citixen/starseq/controller/crc8.cpp

// =============================================================================
//  crc8.cpp — Shared CRC-8 (Dallas/Maxim, polynomial 0x31, init 0x00)
// =============================================================================

#include "crc8.h"

uint8_t crc8(const uint8_t* data, uint8_t len) {
    uint8_t crc = 0x00;
    for (uint8_t i = 0; i < len; i++) {
        crc ^= data[i];
        for (uint8_t b = 0; b < 8; b++) {
            if (crc & 0x80) crc = (crc << 1) ^ 0x31;
            else            crc <<= 1;
        }
    }
    return crc;
}
